ethanhuang03/MobileAirQualitySensor/process_documents/analysis paragraph.docx

Assumptions:
Linkage | $0.6024 / m
Micro-controller | $48.20 / unit
Temperature + Humidity | $2.55 / unit
CO2 | $28.73 / unit
PM 2.5 | $22.86 / unit
VOC | $1.77 / unit
RTC | $3.32 /unit
Room area | 8mx10mx3m, 240m3
Sensor unit (with enough breathing space so air can flow) | 0.027 m3 (30cm*30cm*30cm)

Assume the data and cost estimated is “true” (just not showing the working) and take everything at face-value.

### Current Practice

Current practice for measuring air quality involves the installation of a single sensor in a room or a single sensor per unit squared for outdoor locations. While this approach has several advantages, it also has several limitations that can impact the accuracy of the air quality data.

One of the primary advantages of this approach is its low cost. Each sensor costs less than $108.03, with the wire cost negligible within the sensor unit. This makes it a practical and cost-effective solution for measuring air quality.

Besides being cost-effective, this approach has fast deployment times, with negligible technical issues such as Wi-Fi bandwidth, channel, and data storage. Moreover, the sensors are aesthetically pleasing and do not interfere with usable space, making them suitable for small spaces.

However, this approach also has several limitations. One of the significant drawbacks is that the sensors only provide point measurements, which limits their spatial resolution. Additionally, the effective range of the sensors is limited, and they may not capture changes in air quality in distant locations. The data collected from these sensors only represent the air quality in that exact spot, and they cannot provide information on air quality in multiple directions. Finally, the temporal resolution of the data is limited as the sensors only log data at fixed intervals.

Overall, while this approach to measuring air quality has several advantages, the limitations of the approach mean that it is not always the most accurate or comprehensive solution. To overcome these limitations, increasing the number of sensors and measuring air quality more frequently to obtain a more accurate picture of air quality in a given area.

### Sensor In Every Cubic Inch Of Space Measuring Every Second

The idea of filling an entire room with sensors is to achieve the highest possible spatial resolution for air quality measurements. This involves installing many sensors throughout the room to cover all possible points.

This approach's biggest advantage is its extremely high spatial resolution. Sensors distributed evenly throughout the room make it possible to measure air quality with great precision. Additionally, this approach can record various environmental factors such as temperature, humidity, CO2, PM, and VOC, which can be useful for monitoring and improving indoor air quality.

While this approach has significant advantages in terms of spatial resolution, the cost is a major drawback. Each sensor unit costs $108.03, and 8888 sensors would be required for a single room. The wire required to connect all of these sensors would cost $227.71. This brings the total cost to $960398.35, not including the cost of linking each microcontroller with each other so they can communicate. Furthermore, installing so many sensors in a single room is not practical, as it interferes with the usable space and requires shutting down the room to take measurements.

This approach has gone too far, and the impracticality of filling an entire room with sensors is evident. Instead, it is better to consider more feasible and cost-effective solutions that maintain a good balance between spatial and temporal resolution. Some improvements can be made by reducing the number of sensors required, improving cost-effectiveness, and addressing technical issues such as data storage and communication.

### Sensor Grid Drops Down

The proposed solution involves having many sensor modules hanging from the ceiling of a room, where each sensor module drops down to ground level and winches back up.

This solution offers a similar spatial resolution as the previous option but takes up less space. Additionally, the spatial resolution may increase in the z-axis as the sensor gets continuous data instead of discrete point data.

The cost of this solution is estimated to be $108.03 per sensor. Assuming a ceiling area of 80 m^2, the number of sensors required would be 888, resulting in a total cost of $95,930.64. Each sensor requires at least a 3m long wire, resulting in a total wire length of 2,664m and a total wire cost of $1,604.79. Therefore, the total cost of this solution would be $97,534.79.

The practicality, technical, and cost issues can be addressed by reducing the number of sensors. Although the spatial resolution would decrease, extrapolating the data can still provide a better resolution than the original option and may be good enough for the intended purpose. By reducing the number of sensors, the practicality, technical, and monetary costs can be minimized, making this a more feasible option.

### Sensor Grid in Walls

The proposed solution involves installing a sensor grid on the four walls of a room to measure gas concentrations. The data collected from these sensors will be extrapolated, assuming the properties of gases. This approach reduces the number of sensors required and eliminates the need for continuous measurements.

The primary advantage of this approach is that it requires fewer sensors, making it a more cost-effective solution. It also does not interfere with the usable space in the room, and the installation process is relatively easy. Since the sensors are fixed in specific locations, it provides a reasonable spatial resolution that is good enough for most applications. Additionally, by reducing the number of sensors, it may be possible to increase the temporal resolution, resulting in more frequent measurements.

The total cost for this solution is $3889, assuming 36 sensors are used (9 sensors on 4 walls), and each sensor costs $108.03. The cost of linkage is negligible.

While this solution reduces the number of sensors required, it still involves installing sensors on the walls of a room, which can be impractical and aesthetically unappealing. To improve the solution, it is possible to delocalize the sensors and make them mobile. This approach will enable more flexibility in terms of where the sensors can be placed, making it possible to cover more areas with fewer sensors. The spacial and temporal resolution can be further improved by making the sensors mobile. However, this approach may require more technical resources and higher cost.

### Crowd Sourcing

Air quality sensors are worn by people to gather data as they move around in different locations.

The sensors can collect data only in locations where people go, making the data more useful. The method can easily scale up, providing higher-resolution data with more people in the area. It can be used both indoors and outdoors.

Monetary cost is $108.03 per person equipped with a sensor. Linkage cost is negligible.

Deployment is fast, and the method does not interfere with usable space. Only minor aesthetic changes are required. However, people may get tired from carrying the sensors around.

The method has reduced spatial and temporal resolution due to the random movements of people. People themselves are subject to poor air quality while gathering data. The method is also limited to a certain height.

Bandwidth is sufficient for the task, depending on the number of people equipped with sensors.

Automation of the task can reduce random movements and enable data collection at the entire height of the area.

### Mobile Air Quality Sensor

The mobile air quality sensor is a device that can travel around, usually driven or flown, to measure air quality in different locations. The device is designed to operate outdoors, making it ideal for measuring air pollution in different parts of a city or region.

The mobile air quality sensor offers many advantages over other air quality monitoring systems. First, it eliminates the need for crowd-sourcing data by people, as it can gather data automatically. Second, it offers high mobility, making it easy to take measurements in different locations. Third, it eliminates the disadvantages of crowd-sourcing, such as reduced spatial and temporal resolution and the possibility of people being subject to bad air.

The cost of a mobile air quality sensor can vary depending on the technology used and the features included. However, it will generally be more expensive than a fixed sensor module. In addition to the cost of the device itself, additional costs may be associated with operating the sensor, such as fuel for the vehicle or maintenance costs.

### Concluding remarks

Localised installations of air quality sensors can be costly due to the cubic increase in costs associated with spatial and temporal resolution as the number of sensors is installed. This makes it necessary to compromise by reducing the number of sensors and extrapolating data to reduce costs. However, this approach does not address the fact that localised sensors do not work effectively outdoors. By using mobile air quality sensors, it is possible to overcome this limitation and gather continuous data that is not dependent on people, thus providing higher-resolution spatial measurements and potentially reducing the need for extrapolation.

Mobile air quality sensors are well-suited for outdoor measurements, but a single-point sensor may be sufficient for creating room models and achieving high-resolution measurements for indoor use. However, for daily use, it may not be necessary to install numerous sensors in each room. In terms of business perspectives, the current practice of using localised sensors is the most economical option.
