ethanhuang03/MobileAirQualitySensor/process_documents/Decision.docx

# Decision List

# Assumptions

Assumptions:
Linkage | $0.6024 / m
Micro-controller | $48.20 / unit
Temperature + Humidity | $2.55 / unit
CO2 | $28.73 / unit
PM 2.5 | $22.86 / unit
VOC | $1.77 / unit
RTC | $3.32 /unit
Room area | 8mx10mx3m, 240m3
Sensor unit (with enough breathing space so air can flow) | 0.027 m3 (30cm*30cm*30cm)

# Current Practice

## Descriptions

1. Install a single sensor in a room / Install a single sensor per unit² for outdoor location.

## Advantages

1. Cheap.
  a. Less than $108.03 per sensor (wire cost negligible within the sensor unit)
2. Practicality
  a. Fast deployment
  b. Negilible technical issues (Wifi Bandwidth, Channel and data storage)
  c. Does not interfere with useable space
  d. Aesthetically pleasing
3. Good enough for small spaces.

## Disadvantages

1. Point measurements (spatial resolution limited).
  a. Limited effective range.
  b. Can’t even extrapolate data.
    i. Only useful in one direction
2. Temporal resolution, data is only logged every [time unit]

## How to Improve

To solve the disadvantages, all that is required is to increase the sensor quantity and measure more in a given time.

# Sensor In Every Cubic Inch Of Space Measuring Every Second

## Description

1. Fill the entire room with sensors.

## Advantages

1. Extremely good spatial resolution (highest possible measurements).

## Cost Analysis

1. monetary
  a. $108.03 per sensor.
  b. Quantity of sensor = 240/0.027 = 8888 sensors.
  c. Assume, the wire length to connect the sensor to the board is just the length from the sensor to a designated wall.
    i. Area of wall = 30 m^2
    ii. Number of sensors = 30 m^2 / (30 cm*30cm) = 333
    iii. Sum of wire along the width = 30cm + 60cm + 90cm + … + 810 cm (810 because 800 is not multiple of 30 cm)
      1. 11340 cm = 11.34 m
    iv. Total wire = 11.34 * 10m/30cm = 378m
    v. Total cost = 0.6024*378 = $227.71
  d. Total cost: 108.03*8888 + 227.71 = $960398.35
  e. Excluding wire, costs liking each microcontroller with each other so they can communicate.
2. Practicality
  a. Very slow deployment, having to fit every single sensor into a room and uninstall everything later.
  b. Interferes with useable space. When measuring air quality, no one can use the room.
  c. Aesthetics. Not a problem, as to use the room, the entire system has to be taken out.
  d. Not suitable for outdoor measurements
3. Technical issues
  a. If using WiFi instead of wires, not enough channels (to communicate between sensors).
    i. 2.4 GHz band is broken up into 11 channels (1-11), each 20MHz wide. In the 5 GHz band, we have channels ranging from 36 up to 165, and in the 6 GHz band, we have Wi-Fi channels ranging from 1-233
    ii. Total channels = 233+11+165-33 = 376 < 8888
  b. Storage of data
    i. Recording temperature, humidity, co2, pm, voc.
    ii. Assume they are 32 bit integers
    iii. Every second a sensor records 160 bits
    iv. Total sensor grid records 160*8888 = 1422080 bits per second = 173.59375 KiB per second or 177.76 KB
    v. 1 day of recording = 122.867712 GB of data
    vi. 1 year = 44.8467 TB of data
4. Externalities
  a. So many sensors might even interfere with airflow
  b. Since inhabitants are not in room, it is not an accurate representation of the air flow with people inside

## How to Improve

Reductio ad absurdum. Clearly, this is a solution has gone too far.

Improvements:

1. Literally everything apart from resolution
2. Cost
3. Practicality
4. Tecnical

Basically, how do we accomplish the same results with fewer sensors?

# Sensor Grid Drops Down

## Description

Many sensor modules hang from the ceiling. Each sensor module drops down to ground level and winches back up.

## Advantages

1. Similiar spacial resolution to above.
2. Takes less space
3. Spacial resolution arguably increases in the z axis as the drop down means the sensor is getting continuous data, not discrete point data.

## Cost Analysis

1. monetary
  a. $108.03 per sensor.
  b. Ceiling area is 80 m2
  c. Number of sensor = 80m2/900cm^2 = 888 sensors
  d. $95930.64
  e. Each sensor needs at least 3m long wire
  f. Total wire length = 888*3
  g. Total wire cost = 1604.79
  h. Total cost: 95930+1604.79 = 97534.79
2. Practicality
  a. Slow deployment, have to install a large grind on the ceiling of a room
  b. Still interferes with usable space when sensors are dangling around
  c. Aesthetics, very ugly having a sensor grid mounted on ceiling
  d. Not suitable for outdoor measurements
3. Technical
  a. 2.4 GHz band is broken up into 11 channels (1-11), each 20MHz wide. In the 5 GHz band, we have channels ranging from 36 up to 165, and in the 6 GHz band, we have Wi-Fi channels ranging from 1-233
  b. Total channels = 233+11+165-33 = 376 < 888
  c. If still measuring every second,

## How To Improve

1. We can see that all the practical, technical and cost issues root cause is having too many sensors.
2. Extrapolate data, yes resolution decreases but still better than original and probably good enough, this allows us to reduce practicality, technical and monetary costs.

# Sensor Grid In Walls

Since extrapolating data, we don’t have to fill the entire wall with sensors. Assume 9 sensors per wall, reduce time recording to sampling every hour?

## Description

1. Install a sensor grid on the four walls and extrapolate data, by assuming the properties of gases

## Advantages

1. Fewer sensors used
2. Temporal resolution increases as less sensors means each sensor can afford to measure at a higher rate?

## Disadvantages

1. Data is extrapolated. Some of the resolution is lost. Also depends on size of room. Bigger = worse

## Cost Analysis

1. monetary
  a. 36 sensors, 108.03 per sensor.
  b. $3889
  c. Linkage: negligible
2. Practicality:
  a. Slow deployment. Have to install sensors into the four walls
  b. Does not interfere with usable space
  c. Aesthetics: ugly.
  d. Not suitable for outdoor measurements
3. Technical
  a. Enough bandwidth
  b. Storage not a problem

## How To Improve

Stuff we already compromised on: spacial resolution, temporal resolution.

However, as determined by above, by having sensors fixed in certain location(s), increasing spacial and temporal resolution is not feasible.

To solve this, we can delocalise the sensors and have it mobile.

# Crowd Sourcing

## Description

1. People wear an air quality sensor, and as they walk around, it will gather air quality data in that location.

## Advantage

1. Useful data - no need to measure air quality where people don’t go
2. Easily scaled up, more people in area = more need for higher resolution data, but more people = higher resoluiotn data
3. Works outdoors, indoors and so on.

## Disadvantages

1. Reduced spacial and temporal resolution
1. People’s movements are “random”
2. By gathering data through people, they themselves are subject to bad air if that is a problem
3. People are only limited to a certain height

## Cost Analysis

1. monetary
  a. $108.03 * n where n is the number of people equipped
  b. Linkage - negligible
2. Practicality
  a. Very fast deployment
  b. Does not interfere with usable space
  c. Only minor asethetic changes
  d. People might get tired from carrying sensors around?
3. Technical
  a. Bandwidth is enough dependant on people

## How to improve

Automate this task, so that movement is not random. Make it so that the entire height can be.

# Mobile Air Quality Sensor

## Description

1. A mobile air quality sensor that drives/flies around and does measurements

## Advantages

1. Everything that crowd sources does, but automated and not dependant on people
2. Eliminates disadvantages of crowdsourcing

## Disadavtage

1. Reduced spacial and temporal resolution
2. Asethics, might obstruct indoor usage space.

Justification: this project focuses on outdoor air pollution, mainly while, this is useful for indoor, once one gets a model of the room and identify hotspots, this is not a permanent solution. While outdoors, where current practises do not work as well, it will be permanent.

# Summary

For localised installations, the costs associated with spatial and temporal resolution increase (cubically?) as the number of sensors is installed. The only way, thus compromising, to reduce the cost is by reducing the number of sensors and extrapolating data.

However, this does not address the fact that the sensors are still localised, and does not work outdoors. By having mobile sensors, it is possible to make it work outdoors. Arguably, since the measured data is “continuous” and in motion (thus experiencing different locations), less extrapolation is required and spatial resolution increases. Temporal resolution seems to decrease as we are not measuring the data live when moving around (dead spots). However, compared to when we are extrapolating data, temporal resolution remains the same as above, and arguably still better due to higher resolution spatial measurements. We do a robotic to remove any humans from this operation.

Mobile air quality sensor is “perfect” for outdoor measurements. For indoors, a single-point sensor argument case can be made. If we are studying the room, to create modelling -> high resolution. However, for daily use, do we really need that many sensors?

Resolution: volume ∝ 1/resolution

Localised: sensor∝cost^3

THrough analysis we can see from a business perspective, current practise is the most economical
