ethanhuang03/MobileAirQualitySensor/images/drone front.jpg

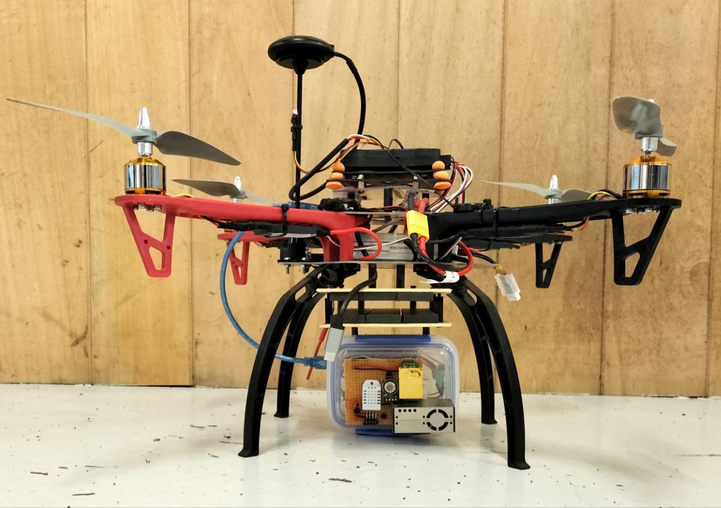
images/drone front.jpg
