ethanhuang03/MobileAirQualitySensor/images/IMG20230910210008.jpg

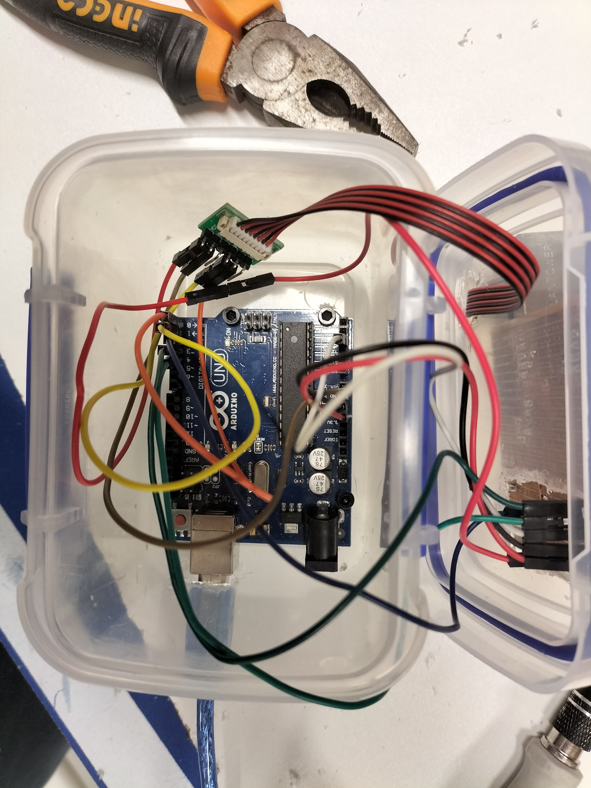
images/IMG20230910210008.jpg
