ethanhuang03/MobileAirQualitySensor/images/IMG20230910210015.jpg

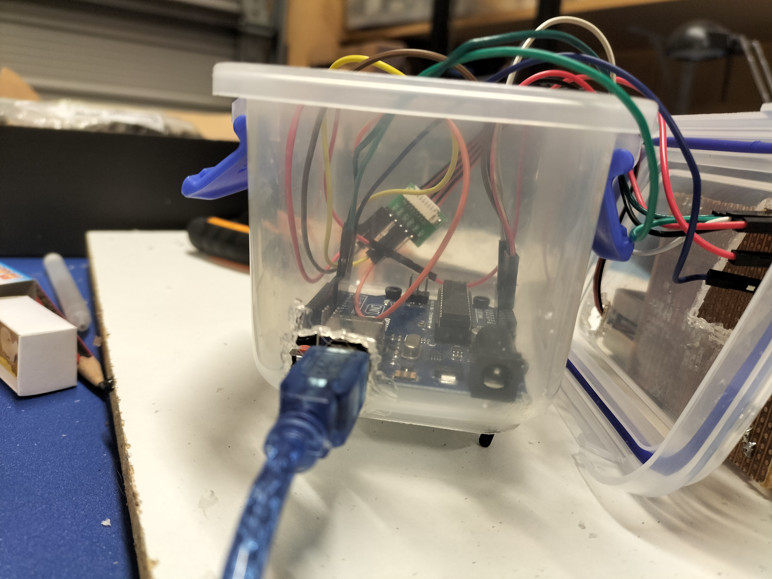
images/IMG20230910210015.jpg
