ethanhuang03/MobileAirQualitySensor/images/IMG20230910210036.jpg

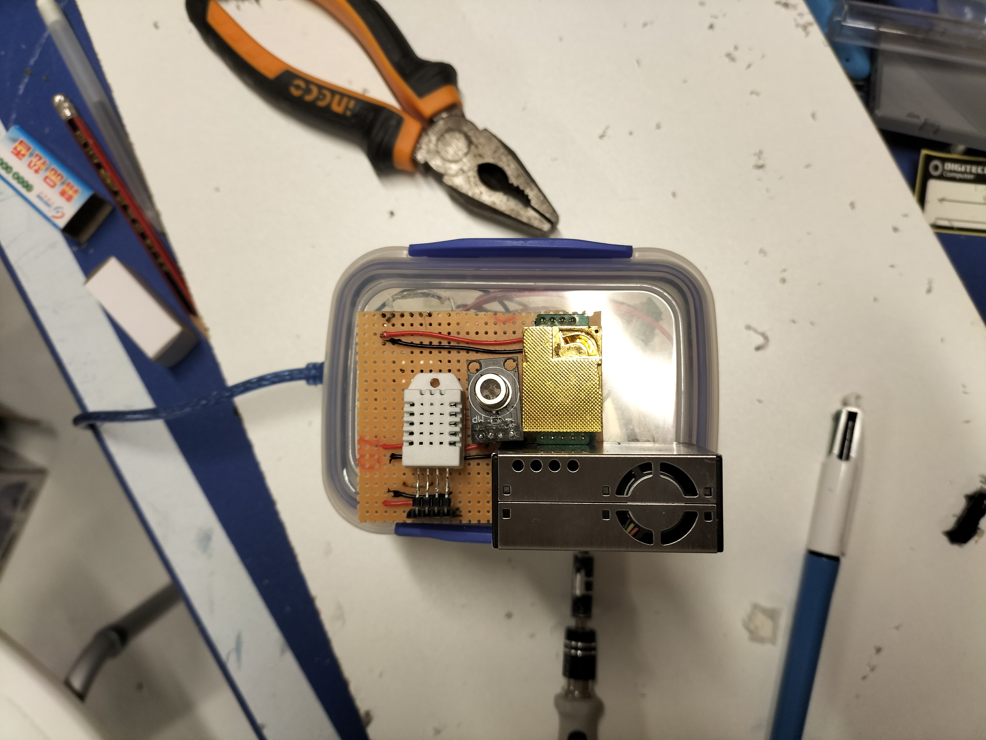
images/IMG20230910210036.jpg
