ethanhuang03/MobileAirQualitySensor/images/IMG20230917164229.jpg

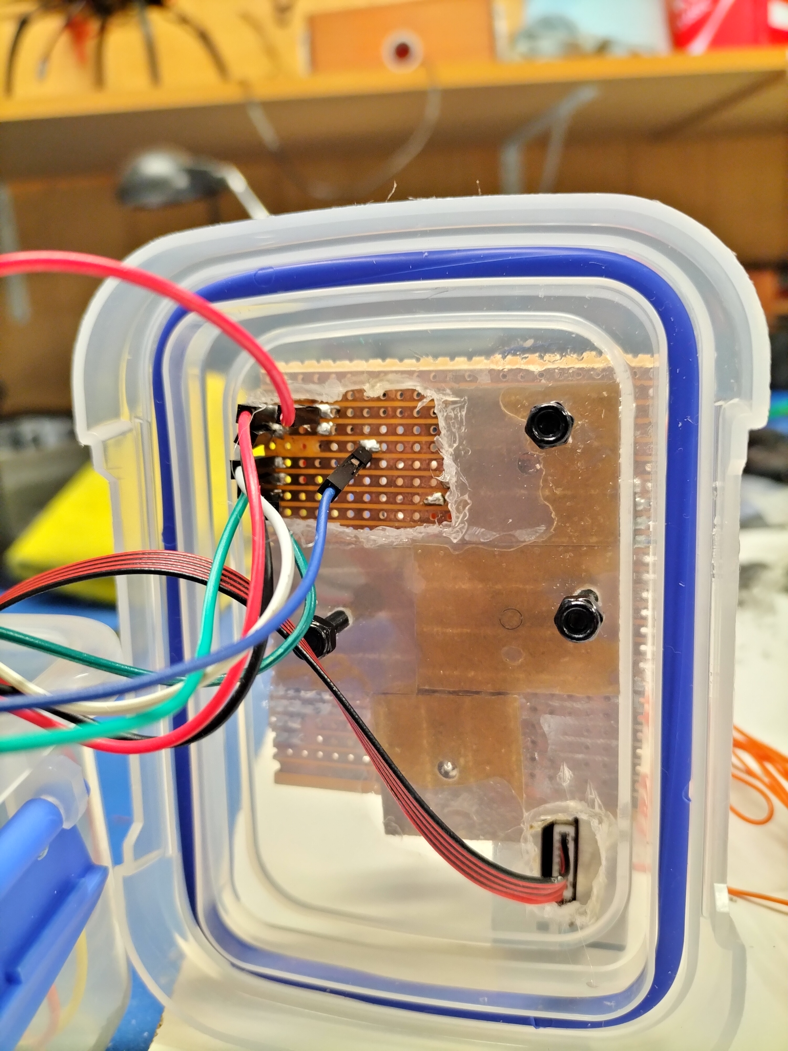
images/IMG20230917164229.jpg
