ethanhuang03/MobileAirQualitySensor/images/IMG20230917181914.jpg

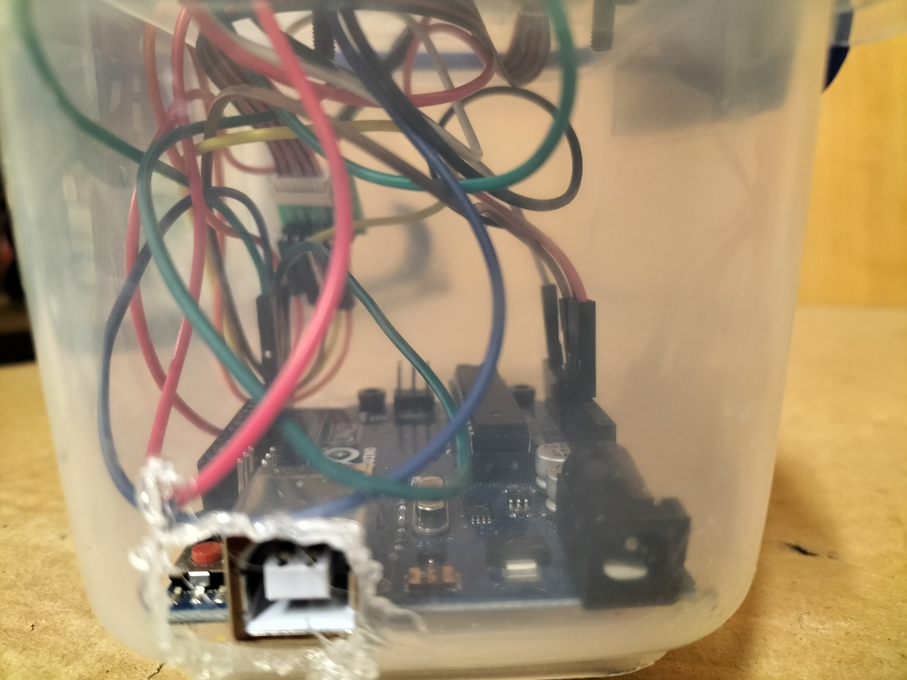
images/IMG20230917181914.jpg
