ethanhuang03/MobileAirQualitySensor/images/IMG20230917182846.jpg

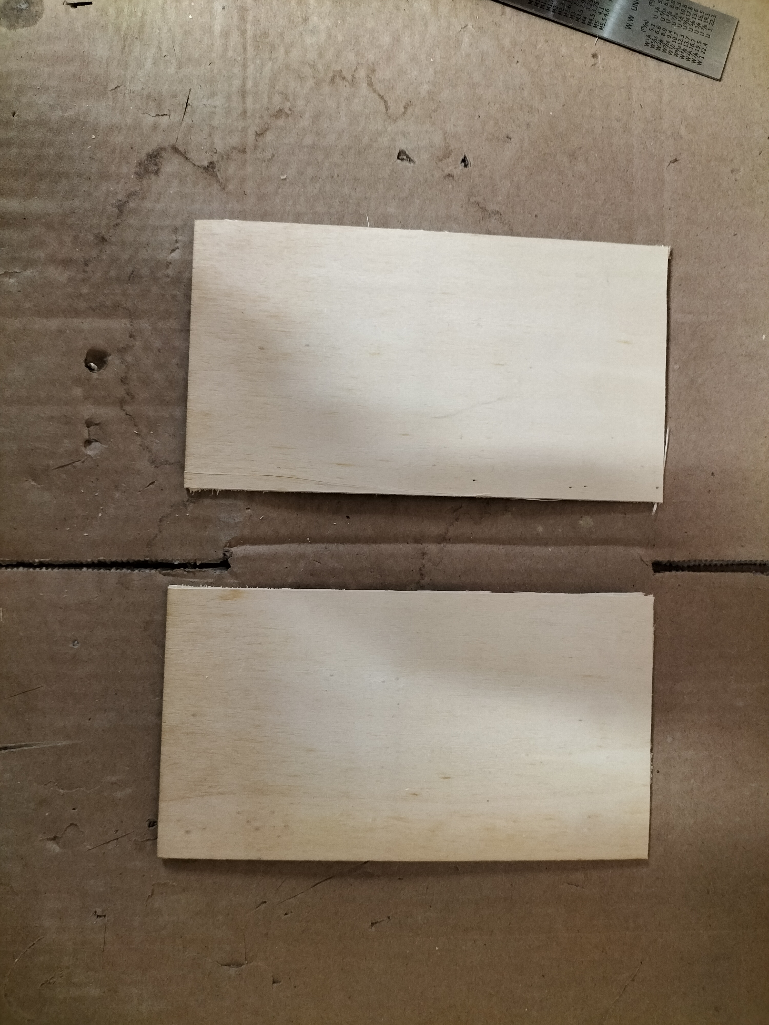
images/IMG20230917182846.jpg
