ethanhuang03/MobileAirQualitySensor/images/IMG20230924164048.jpg

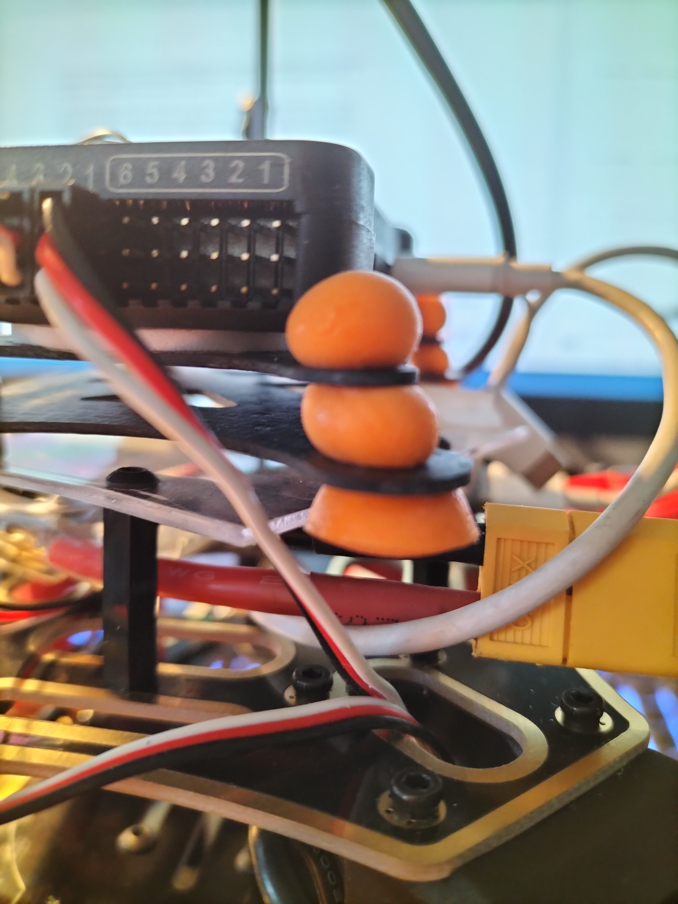
images/IMG20230924164048.jpg
