ethanhuang03/MobileAirQualitySensor/images/initial_prototype2.jpg

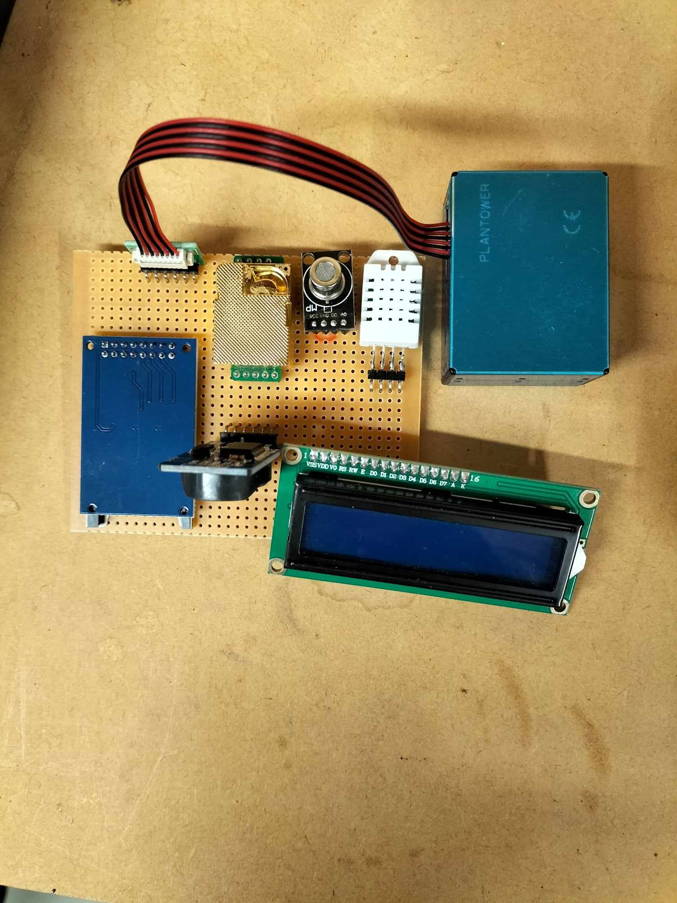
images/initial_prototype2.jpg
