ethanhuang03/MobileAirQualitySensor/images/ormiston_model.jpg

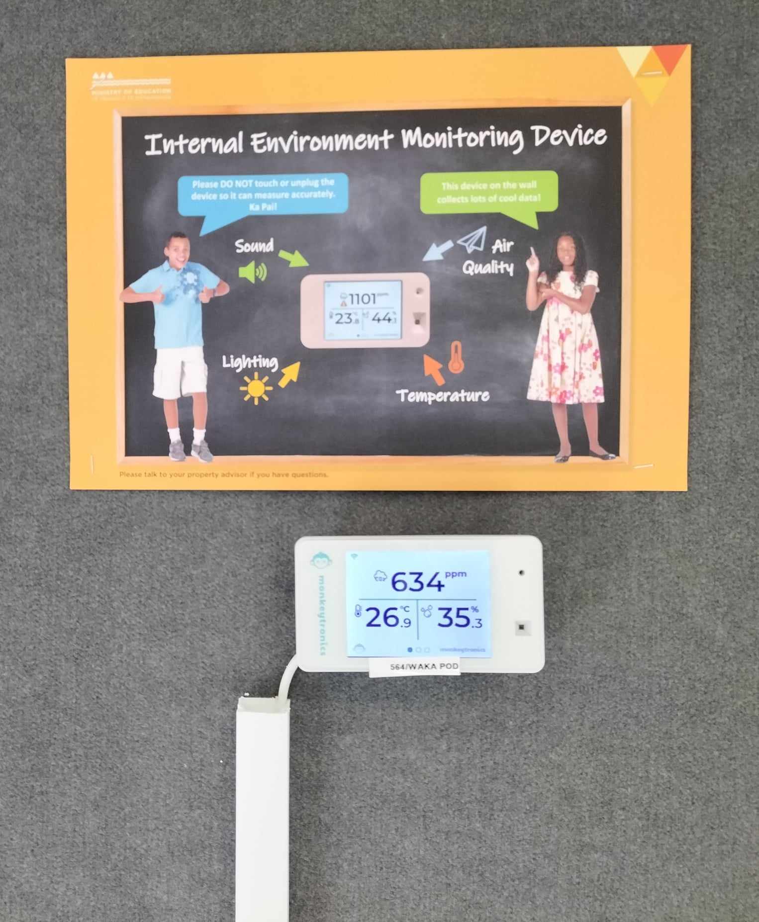
images/ormiston_model.jpg
