ethanhuang03/MobileAirQualitySensor/images/phoneholder2.jpg

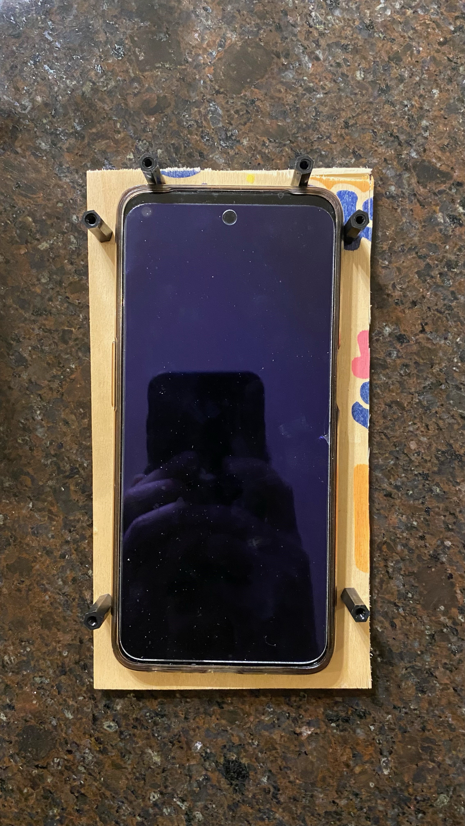
images/phoneholder2.jpg
